te9no/Geacon/docs/img/1.jpg

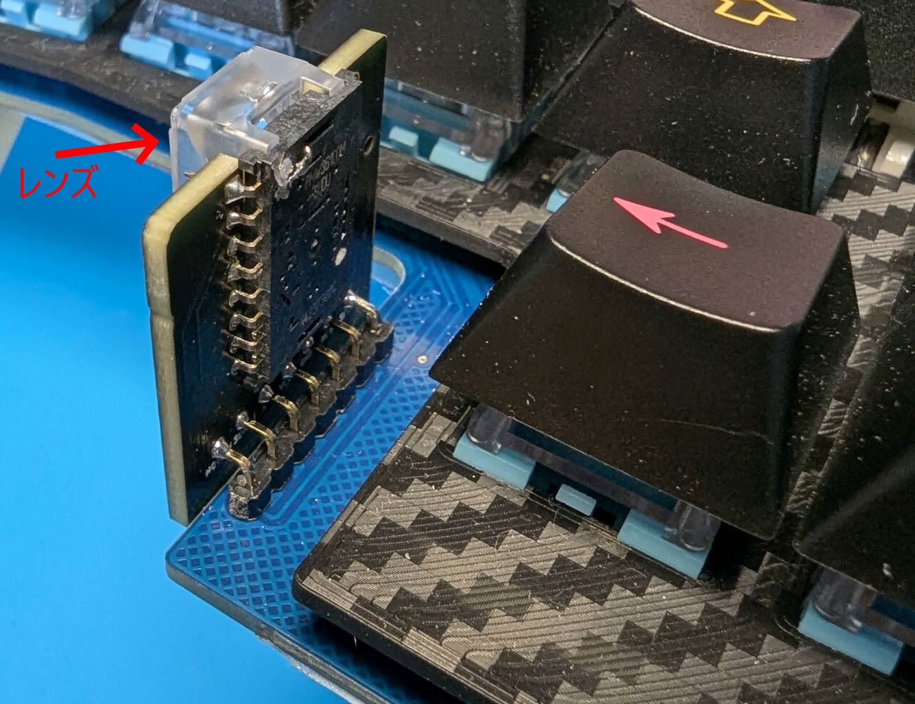
docs/img/1.jpg
