te9no/Geacon/docs/img/2.jpg

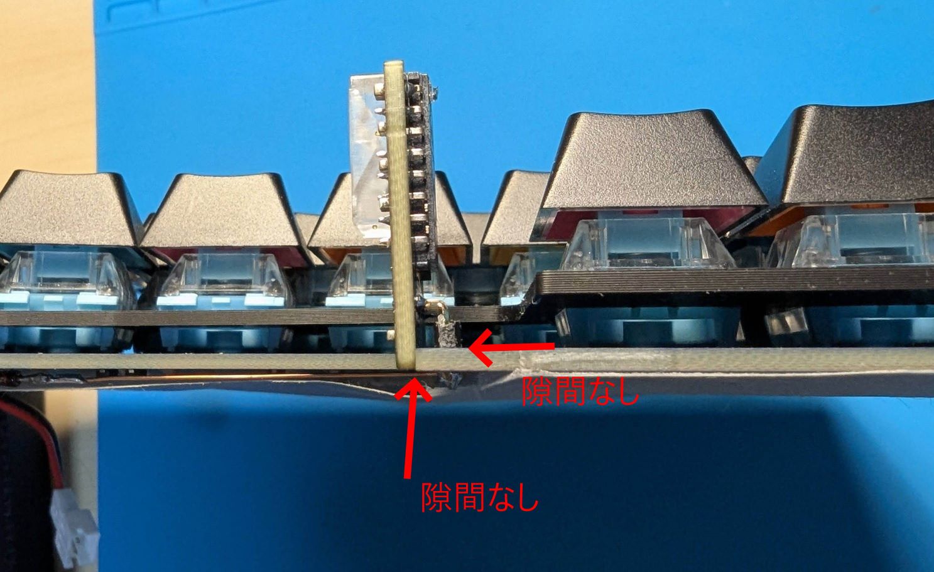
docs/img/2.jpg
